Alp-1/GDP_software/CAD Models/Individual Parts/Makerbeams/eye_plate_gs3212-05.stp

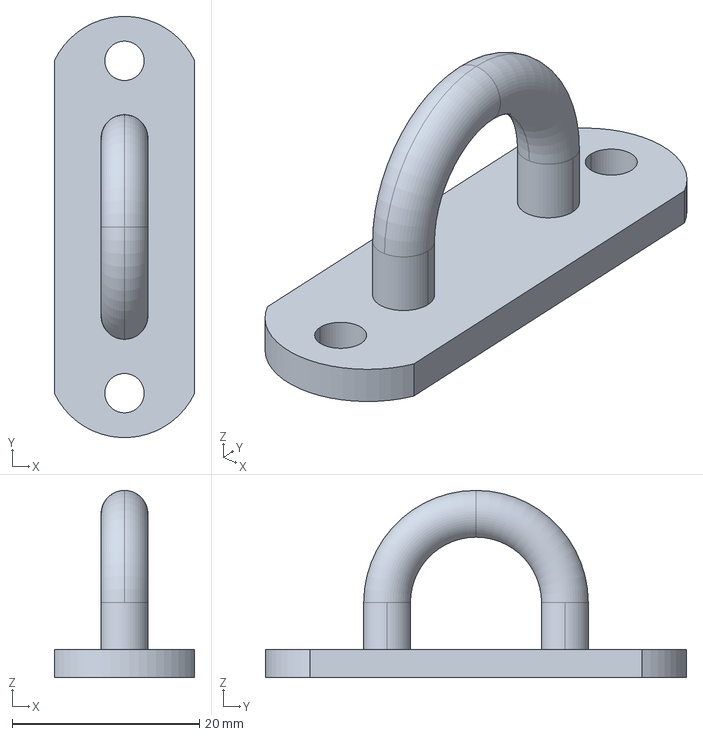
[picture p15: CAD file, 2024-10-24]
CAD Models/Individual Parts/Makerbeams/eye_plate_gs3212-05.stp
15.0 x 45.0 x 20.0 mm
