Alp-1/GDP_software/navigation/steering_basic.py

import math
import time
import numpy as np
import cv2
from pyrealsense import pyrealsense2 as rs
import json
from pymavlink import mavutil
# from dronekit import connect, VehicleMode, LocationGlobalRelative
from dronekit import *
import mav_listener
# Connect to the vehicle
mavlink_connection = mavutil.mavlink_connection('/dev/ttyAMA0', baud=57600)
mavlink_connection.wait_heartbeat()
print("Heartbeat from MAVLink system (system %u component %u)" % (
mavlink_connection.target_system, mavlink_connection.target_component))
vehicle = connect('/dev/ttyAMA0', wait_ready=False, baud=57600)

# Threshold for what we consider an obstacle (in meters)
obstacle_threshold = 1.0

def send_ned_velocity(velocity_x, velocity_y, velocity_z, duration):
    """
    Move vehicle in direction based on specified velocity vectors.
    """
    msg = vehicle.message_factory.set_position_target_local_ned_encode(
        0,       # time_boot_ms (not used)
        0, 0,    # target system, target component
        mavutil.mavlink.MAV_FRAME_BODY_OFFSET_NED, # frame
        0b0000111111000111, # type_mask (only speeds enabled)
        0, 0, 0, # x, y, z positions (not used)
        velocity_x, velocity_y, velocity_z, # x, y, z velocity in m/s
        0, 0, 0, # x, y, z acceleration (not supported yet, ignored in GCS_Mavlink)
        0, 0)    # yaw, yaw_rate (not supported yet, ignored in GCS_Mavlink)

    # send command to vehicle on 1 Hz cycle
    for x in range(0,duration):
        vehicle.send_mavlink(msg)
        time.sleep(1)

def send_ned_yaw_pymavlink(velocity_x, velocity_y, velocity_z, yaw, duration):
    """
    Move vehicle in direction based on specified velocity vectors using pymavlink.
    """
    for _ in range(duration):
        mavlink_connection.mav.set_position_target_local_ned_send(
            0,  # time_boot_ms (not used)
            mavlink_connection.target_system,  # target system
            mavlink_connection.target_component,  # target component
            mavutil.mavlink.MAV_FRAME_BODY_OFFSET_NED,  # frame
            0b0000111111000111,  # type_mask (only speeds enabled)
            0, 0, 0,  # x, y, z positions (not used)
            velocity_x, velocity_y, velocity_z,  # x, y, z velocity in m/s
            0, 0, 0,  # x, y, z acceleration (not supported yet, ignored in GCS_Mavlink)
            math.radians(yaw), 0)  # yaw, yaw_rate
        time.sleep(1)

def send_ned_yaw_pymavlink_once(velocity_x, velocity_y, velocity_z, yaw):
    """
    Move vehicle in direction based on specified velocity vectors using pymavlink.
"""
    mavlink_connection.mav.set_position_target_local_ned_send(
        0,  # time_boot_ms (not used)
        mavlink_connection.target_system,  # target system
        mavlink_connection.target_component,  # target component
        mavutil.mavlink.MAV_FRAME_BODY_OFFSET_NED,  # frame
        0b100111111111,  # type_mask (only speeds enabled)
        0, 0, 0,  # x, y, z positions (not used)
        velocity_x, velocity_y, velocity_z,  # x, y, z velocity in m/s
        0, 0, 0,  # x, y, z acceleration (not supported yet, ignored in GCS_Mavlink)
        math.radians(yaw), 0)  # yaw, yaw_rate

def send_ned_pymavlink(velocity_x, velocity_y, velocity_z):
    mavlink_connection.mav.set_position_target_local_ned_send(
        0,  # time_boot_ms (not used)
        mavlink_connection.target_system,  # target system
        mavlink_connection.target_component,  # target component
        mavutil.mavlink.MAV_FRAME_BODY_OFFSET_NED,  # frame
        0b110111100111 ,  # type_mask (only speeds enabled)
        0, 0, 0,  # x, y, z positions (not used)
        velocity_x, velocity_y, velocity_z,  # x, y, z velocity in m/s
        0, 0, 0,  # x, y, z acceleration (not supported yet, ignored in GCS_Mavlink)
        0, 0)  # yaw, yaw_rate

def spin_rover(duration, left_speed, right_speed):
    
    start_time = time.time()
    while time.time() - start_time < duration:
        left_speed = 1200
        right_speed = 1500
        override_rc_channels(left_speed,right_speed,0,0)
        time.sleep(0.1)

    # Stop the rover after spinning
    override_rc_channels(1500, 1500, 0, 0)

def wait_for_turn_completion(yaw_angle, turn_rate=30):
    """
    Wait for the rover to complete its turn.

    Parameters:
    yaw_angle (float): The yaw angle in degrees.
    turn_rate (float): Estimated turn rate in degrees per second.
    """
    turn_time = abs(yaw_angle / turn_rate)
    send_ned_yaw_pymavlink(0, 1, 0, 90, turn_time)
    

def turn_rover(yaw_angle, relative=True):
    """
    Turn the rover by a specified angle.

    Parameters:
    yaw_angle (float): The yaw angle in degrees. Positive values turn right, negative values turn left.
    relative (bool): If True, the turn is relative to the current heading.
    """
    set_yaw_angle(yaw_angle, relative)
    wait_for_turn_completion(yaw_angle)



def set_yaw_angle(yaw_angle, relative=False):
    """
    Set the yaw angle of the vehicle.

    Parameters:
    yaw_angle (float): The yaw angle in degrees.
    relative (bool): Set to True if the provided yaw angle is relative to the current heading.
    """
    if relative:
        is_relative = 1  # yaw relative to direction of travel
    else:
        is_relative = 0  # yaw is an absolute angle

    # Convert yaw angle to a valid range
    yaw_angle = yaw_angle % 360

    # Send COMMAND_LONG to set the yaw angle
    mavlink_connection.mav.command_long_send(
        mavlink_connection.target_system,  # target_system
        mavlink_connection.target_component,  # target_component
        mavutil.mavlink.MAV_CMD_CONDITION_YAW,  # command
        0,  # confirmation
        yaw_angle,  # param 1: yaw angle in degrees
        0,  # param 2: yaw speed (not used)
        1,  # param 3: direction (-1: CCW, 1: CW)
        is_relative,  # param 4: relative or absolute
        0, 0, 0  # params 5-7 (not used)
    )

# Function to be called whenever HEARTBEAT messages are received
def heartbeat_listener(self, name, message):
    print("Heartbeat received")
    print("Base Mode: {}".format(message.base_mode))
    print("Custom Mode: {}".format(message.custom_mode))

# Add the listener for the heartbeat message
#vehicle.add_message_listener('HEARTBEAT', heartbeat_listener)
# Global variable for the RealSense profile
profile = None


# Function to override RC channels
# def override_rc(channels):
#     channel_values = [0] * 8  # there are eight RC channels on most systems
#     for channel, value in channels.items():
#         channel_values[channel - 1] = value  # channels are 1-indexed in MAVLink
#     vehicle.channels.overrides = channel_values


#Create a message listener for all messages.
# @vehicle.on_message('*')
def listener(self, name, message):
    print ('message: %s' % message)


# Function to clear RC overrides
def override_rc_channels(ch1, ch2, ch3, ch4):
    """
    Override RC channels using pymavlink.
    ch1, ch2, ch3, ch4: Channel values (1000 to 2000)
    """
    mavlink_connection.mav.rc_channels_override_send(
        mavlink_connection.target_system,  # target_system
        mavlink_connection.target_component,  # target_component
        ch1, ch2, ch3, ch4, 0, 0, 0, 0)  # channels 1-8 (set channels 5-8 to 0)



# Initialize RealSense pipeline and profile
def initialize_realsense():
    global profile
    pipeline = rs.pipeline()
    config = rs.config()
    config.enable_stream(rs.stream.color, 848, 480, rs.format.bgr8, 60)  # RGB stream
    config.enable_stream(rs.stream.depth, 848, 480, rs.format.z16, 60)  # Depth stream
    config.enable_stream(rs.stream.accel, rs.format.motion_xyz32f, 200)  # Accelerometer data
    config.enable_stream(rs.stream.gyro, rs.format.motion_xyz32f, 400)  # Gyroscope data
    profile = pipeline.start(config)

    sensor = profile.get_device().query_sensors()[1]
    sensor.set_option(rs.option.enable_auto_exposure, False)
    sensor.set_option(rs.option.exposure, 78.0)
    sensor.set_option(rs.option.gain, 90.0)

    depth_sensor = profile.get_device().query_sensors()[0]
    # depth_sensor.set_option(rs.option.visual_preset,4) #high density preset, medium density is 5. doesn't work rn, maybe because of no advanced mode on pi?
    return pipeline, profile


def apply_filters(depth_frame):
    decimation = rs.decimation_filter()
    spatial = rs.spatial_filter()
    spatial.set_option(rs.option.holes_fill, 5)  # do I still need hole filling???
    hole_filling = rs.hole_filling_filter(2)  # use min of neighbour cells,might need changing
    threshold_filter = rs.threshold_filter(0.3, 4.0)
    depth_to_disparity = rs.disparity_transform(True)
    disparity_to_depth = rs.disparity_transform(False)

    # spatial.set_option(rs.option.holes_fill, 3) #try 5??
    frame = depth_frame
    frame = threshold_filter.process(frame)
    frame = decimation.process(frame)
    frame = depth_to_disparity.process(frame)
    frame = spatial.process(frame)
    frame = disparity_to_depth.process(frame)
    frame = hole_filling.process(frame)
    return frame


def get_new_images():
    frames = pipeline.wait_for_frames()
    depth_frame = frames.get_depth_frame()
    color_frame = frames.get_color_frame()
    if not depth_frame or not color_frame:
        print("problems")

    color_image = np.asanyarray(color_frame.get_data())
    depth_frame = apply_filters(depth_frame)
    depth_image = np.asanyarray(depth_frame.get_data()) * depth_scale

    # num_zeros = np.count_nonzero(depth_image == 0)
    # print(f"Number of zero values in depth image:{num_zeros}")
    return depth_image, color_image


# Specify the width of the rover in meters
rover_width = 0.5  # Adjust to your rover's width

def obstacle_ahead(depth_image, depth_scale):
    depth_image= depth_image * depth_scale

    # Calculate the size of the central square
    central_width = depth_image.shape[1] // 3
    central_height = depth_image.shape[0] // 4

    # Calculate the starting indices for the central square
    start_row = (depth_image.shape[0] - central_height) // 2
    start_col = (depth_image.shape[1] - central_width) // 2

    # Select the central square
    central_square = depth_image[start_row:start_row + central_height, start_col:start_col + central_width]

    # Create a masked array where 0 values are masked
    masked_array = np.ma.masked_where(central_square == 0, central_square)

    # Find the minimum value while excluding masked values (0s)
    min_value_without_zeros = np.min(masked_array)
    if min_value_without_zeros<obstacle_threshold:
        return True
    else:
        return False

# Function to find a clear path and calculate its direction
def find_clear_path_and_calculate_direction(depth_image, depth_scale, rover_width):
    # Convert depth image to meters
    depth_image_meters = depth_image * depth_scale

    # Threshold for what we consider an obstacle (in meters)
    column_means = np.mean(depth_image_meters, axis=0)
    # Find the index of the column with the highest mean
    index_of_highest_mean = np.argmax(column_means)
    angle = index_of_highest_mean / len(column_means) * 87 - (87 / 2)
    if angle>=0:
        yaw_angle = math.radians(angle)
    else:
        yaw_angle = math.radians(angle+360)
        
    # if angle>=0:
        # yaw_angle = angle
    # else:
        # yaw_angle = 360 + angle
    return yaw_angle

vegetation_threshold = 0.017
def detect_tall_vegetation(depth_image, depth_scale, vegetation_height_threshold):
    """
    Detect tall vegetation in the path using a RealSense depth image.

    Parameters:
    depth_image (ndarray): The depth image from the RealSense camera.
    depth_scale (float): The scale to convert depth units to meters.
    vegetation_height_threshold (float): The minimum height (in meters) to consider as vegetation.

    Returns:
    bool: True if tall vegetation is detected, False otherwise.
    """
    vegetation_height_threshold = 0.2 
    # Convert depth image to meters
    # depth_in_meters = depth_image * depth_scale
    depth_in_meters = depth_image
    # Define the region of interest (ROI) in the image
    # For example, you might want to focus on the lower part of the image
    roi_start_row = int(depth_in_meters.shape[0] * 0.5)  # Starting from the middle row
    roi_end_row = depth_in_meters.shape[0]  # To the end of the image
    roi = depth_in_meters[roi_start_row:roi_end_row, :]

    # Find areas in the ROI where the depth suddenly changes
    # This can be done by calculating the gradient and looking for large changes
    depth_gradient = np.abs(np.gradient(roi, axis=0))
    vegetation_mask = depth_gradient > vegetation_height_threshold

    # Detect vegetation if there are significant changes in depth
    vegetation_detected = np.any(vegetation_mask)
    print("detected")
    return vegetation_detected

def move_back(steps):
    """
    Move the rover back by a certain number of steps.
    """
    for _ in range(steps):
        send_ned_velocity(-1, 0, 0, 1)
            
# Function to navigate while avoiding obstacles
def navigate_avoiding_obstacles(depth_scale):
    obstacle_threshold = 1.0
    frames = pipeline.wait_for_frames()
    depth_frame = frames.get_depth_frame()
    if not depth_frame:
        return

    depth_image = np.asanyarray(depth_frame.get_data())
    print(vehicle.mode.name)
    if vehicle.mode.name == "AUTO" or vehicle.mode.name == "GUIDED":
        if detect_tall_vegetation(depth_image, depth_scale):
            print("Tall vegetation detected. Moving back.")
            vehicle.mode = VehicleMode("GUIDED")
            move_back(2)  # Move back 2 steps
        else:
            if obstacle_ahead(depth_image,depth_scale):
                vehicle.mode = VehicleMode("GUIDED")
                clear_path_direction = find_clear_path_and_calculate_direction(depth_image, depth_scale, rover_width)
            #print(clear_path_direction)
         
                print("obstacle ahead")
#                 current_heading = vehicle.heading

#         # Calculate new heading: turn left by 90 degrees
#                 new_heading = (current_heading + 90) % 360
#                 # Example usage
#                 # Example usage: Spin the rover for 5 seconds
# # Assuming 1000 is full reverse, 1500 is stop, and 2000 is full forward.
#                 # spin_rover(5, 1000, 2000) 

#         # Set the new yaw angle
#                 set_yaw_angle(new_heading, relative=False)

#         # Move with the specified NED velocity while turning
#                 send_ned_yaw_pymavlink(0, 1, 0, new_heading, 5)
            # send_ned_velocity(1,0,0,5)
            else:
                print("no obstacle ahead")
                vehicle.mode = VehicleMode("AUTO")
                override_rc_channels(1600, 1500, 0, 0)  # Override throttle and steering channels
import time

def detect_collision(mavlink_connection):
    """
    Detects collision by comparing rover speed from MAVLink and optical flow data.
    """
    start_time = time.time()
    collision_detected = False

    while time.time() - start_time < 5:
        # Retrieve speed data from MAVLink
        current_speed = mav_listener.get_rover_speed(mavlink_connection)  # Speed in cm/s
        print(f"speeeed:{current_speed}")
        # Retrieve optical flow data from MAVLink
        optical_flow_data = get_optical_flow_data_from_mavlink()
        print(optical_flow_data)
        # Check for near-zero optical flow and non-zero speed
        if is_near_zero(optical_flow_data) and current_speed > 0:
            collision_detected = True
            break
        time.sleep(0.1)  # Adjust time interval as needed

    if collision_detected:
        print("Collision detected. Reversing and finding another path.")
        # Implement actions after detecting collision, e.g., move_back, find_alternate_path, etc.

def is_near_zero(data, threshold=0.1):
    """
    Check if data is near zero within a given threshold.
    """
    x, y = data
    return abs(x) < threshold and abs(y) < threshold

def get_optical_flow_data_from_mavlink():
    """
    Retrieve optical flow data from MAVLink.
    """
    # Fetch optical flow data from a relevant MAVLink message
    # Example: Use flow_x and flow_y for optical flow data
    optical_flow_msg = mavlink_connection.recv_match(type='OPTICAL_FLOW', blocking=True)
    if optical_flow_msg:
        return optical_flow_msg.flow_x, optical_flow_msg.flow_y
    else:
        return 0, 0

# Implement move_back() and find_alternate_path() as needed


def wheels_are_spinning():
    left_dist1, right_dist1 = mav_listener.get_wheel_distances(mavlink_connection)
    time.sleep(0.05)
    left_dist2, right_dist2 = mav_listener.get_wheel_distances(mavlink_connection)
    left_diff = left_dist2 - left_dist1
    right_diff = right_dist2 - right_dist1
    print(f"Wheel distance difference in 50ms: {left_diff} {right_diff}")
    if left_diff>0.02 or right_diff>0.02:
        return True
    else:
        return False

def is_tall_vegetation(depth_image,speed):
    percentage_threshold = 0.5
    nr_of_pixels = depth_image.size
    print(nr_of_pixels)
    percentage = np.count_nonzero(depth_image==0) / nr_of_pixels
    print(f"percentage of pixels with 0 value:{percentage}")
    if percentage>percentage_threshold and speed > 0.35:
        return True
    else:
        return False


def is_collision(speed):
    if speed < 0.25 and wheels_are_spinning():
        return True
    else:
        return False



def calculate_distance(depth_image, y1, x1, y2, x2):
    # udist = depth_frame.get_distance(x1, y1)
    # vdist = depth_frame.get_distance(x2, y2)
    udist = depth_image[y1, x1]
    vdist = depth_image[y2, x2]

    point1 = rs.rs2_deproject_pixel_to_point(depth_intrinsics, [y1, x1], udist)
    point2 = rs.rs2_deproject_pixel_to_point(depth_intrinsics, [y2, x2], vdist)

    # euclidean distance between two points, measured in meters
    dist = math.sqrt(
        math.pow(point1[0] - point2[0], 2) + math.pow(point1[1] - point2[1], 2) + math.pow(
            point1[2] - point2[2], 2))
    # result[0]: right, result[1]: down, result[2]: forward
    return dist


def gap_size(depth_image, column):
    gap_threshold = 0.4
    # start_row = depth_image.shape[0] // 2
    width_left = column
    width_right = column
    height_up = depth_image.shape[0] // 2

    square_height = depth_image.shape[0] // 10
    # square_width = column_width
    start_row = (depth_image.shape[0] - square_height) // 2
    end_row = start_row + square_height
    gap_width = 9999.0
    for row in range(start_row, end_row+1):
        width_left = column
        width_right = column
        if depth_image[row,column] != 0:
            while width_left > 1:
                difference = depth_image[row, width_left] - depth_image[row, width_left - 1]
                if difference > gap_threshold and depth_image[row, width_left - 1] < (2 * obstacle_threshold) and \
                        depth_image[row, width_left - 1] < depth_image[row, column] and depth_image[row, width_left - 1] !=0:
                    break
                else:
                    width_left -= 1
            width_left -= 1

            while width_right < (depth_image.shape[1] - 2):
                difference = depth_image[row, width_right] - depth_image[row, width_right + 1]
                if difference > gap_threshold and depth_image[row, width_right + 1] < (2 * obstacle_threshold) and \
                        depth_image[row, width_right + 1] < depth_image[row, column] and depth_image[row, width_right + 1]!=0:
                    break
                else:
                    width_right += 1
            width_right += 1
            width = calculate_distance(depth_image, row, width_left, row, width_right)
            gap_width = min(width,gap_width)

    while height_up > 1:
        difference = depth_image[height_up, column] - depth_image[height_up - 1, column]
        if difference > gap_threshold and depth_image[height_up - 1, column] < (2 * obstacle_threshold) and depth_image[
            height_up - 1, column] < depth_image[row, column] and depth_image[height_up - 1, column] != 0:
            break
        else:
            height_up -= 1
    height_up -= 1

    gap_height = calculate_distance(depth_image, row, column, height_up, column)
    print(f"gap boundary pixels:{width_left} {width_right}")
    print(f"GAP: height from camera:{gap_height} width:{gap_width}")
    return gap_height, gap_width


# Main execution loop
try:
    pipeline, profile = initialize_realsense()
    depth_sensor = profile.get_device().first_depth_sensor()
    depth_scale = depth_sensor.get_depth_scale()

    frames = pipeline.wait_for_frames()
    prof = frames.get_profile()
    depth_intrinsics = prof.as_video_stream_profile().get_intrinsics()
    print("Depth Scale is: ", depth_scale)
    detect_collision(mavlink_connection)
    vehicle.armed = True
    # turn_rover(90, relative=True)
    print(vehicle.mode)
    while True:
        current_speed = mav_listener.get_rover_speed(mavlink_connection)
        current_speed /= 100
        print(f"current speed:{current_speed}")

        depth_image,color_image = get_new_images()
        if is_tall_vegetation(depth_image,current_speed):
            print("TALL VEGETATION")

        if is_collision(current_speed):
            print("COLLISION")
        gap_size(depth_image,depth_image.shape[1]//2)
        # if both -> go back abit. if only one of the, different
        # how to interpret encoder data
        # detect_collision(mavlink_connection)
        # detect_tall_vegetation(depth_image,depth_scale,0.017)

        time.sleep(0.2)
except KeyboardInterrupt:
    print("Script terminated by user")

finally:
    # clear_rc_overrides()
    pipeline.stop()
    cv2.destroyAllWindows()
    vehicle.close()
    mavlink_connection.close()
    print("Connection closed.")
