Alp-1/GDP_software/low_level_control/motor_controller/motor_sensor.py

from machine import Pin, ADC

from motor_controller.encoder import Encoder


class MotorSensing:
    """Class to sense the parameters of a motor"""

    PPR = 2448  # Pulses per revolution of the encoder (12*4*51)

    def __init__(
        self,
        encoder_out_A: int,
        sm_no: int,
        adc_in: int,
        invert_current: bool = False,
    ):
        """Initialise motor feedback components.

        Parameters
        ----------
        encoder_out_A: int
            The output A of the encoder.
            The second pin (Output B) is assumed to be encoder_out_A + 1
        sm_no: int
            The state machine number to use for the encoder pio
        adc_in: int
            The ADC pin to use for current sensing
        invert_current: bool
            Set to True if the current sensor is inverted

        """
        # Define the pins for the inputs
        ENCODER_OUT_A = Pin(encoder_out_A, Pin.IN, Pin.PULL_DOWN)
        self.encoder = Encoder(sm_no, ENCODER_OUT_A)
        self.current_sensor = ADC(adc_in)
        self.invert_current = invert_current

        self.no_of_samples = 256 * 4
        self.offset_u16 = 0
        self.calibrate_adc()

    def calibrate_adc(self):
        """Calibrate the ADC by finding the zero current adc val
        (i.e. the midpoint of the adc range in theory)
        """
        average_u16 = 0
        for _ in range(self.no_of_samples):
            average_u16 += self.current_sensor.read_u16()
        self.offset_u16 = average_u16 / self.no_of_samples

    @property
    def rpm(self):
        result = self.encoder.freq() * 60 / self.PPR
        # print("Freq: {}".format(self.encoder.freq()))
        # print("RPM: {}".format(result))
        return result

    @property
    def current(self):
        """Get the current of the motor (A).

        For ACS711EX (+-31A), the sensitivity is 45 mV/A for 3.3V supply.

        45mV/A is derived from 3.3V/73.3A (Refer to https://www.pololu.com/product/2453)

        Perform averaging for better accuracy.
        """

        average_u16 = 0
        for _ in range(self.no_of_samples):
            average_u16 += self.current_sensor.read_u16()
        average_u16 /= self.no_of_samples
        vout = (average_u16 - self.offset_u16) * 3.3 / 65535
        if self.invert_current:
            vout = -vout
        return vout / 0.045
