Alp-1/GDP_software/low_level_control/central_hub/main.py

from central_hub.central_hub import main
import asyncio

while True:
    try:
        asyncio.run(main())
    except Exception as e:
        print(e)
    finally:
        print(asyncio.current_task().coro)
        asyncio.new_event_loop()
