Alp-1/GDP_software/navigation/geometric_map.py

import copy
import math

import open3d as o3d
import numpy as np
from pyrealsense import pyrealsense2 as rs
import time
import scipy
import cv2
# cell_height = 120
# cell_width = 212
# grid_n = 4
# grid_m = 4
from matplotlib import pyplot as plt

# cell_height = 60
# cell_width = 106 #miert??
grid_n = 1
grid_m = 4

#!!!changed: 10x10 grid
def direction_to_euler_angles(direction):
    # Normalize the direction vector
    normalized_direction = direction / np.linalg.norm(direction)

    # Calculate pitch angle
    pitch_rad = np.arcsin(normalized_direction[2])
    pitch_deg = np.degrees(pitch_rad)

    # Calculate yaw angle
    yaw_rad = np.arctan2(normalized_direction[1], normalized_direction[0])
    yaw_deg = np.degrees(yaw_rad)

    return pitch_deg, yaw_deg

def get_slope_grid(depth_image,depth_intrinsics,angles):
    rotation_matrix = o3d.geometry.get_rotation_matrix_from_zyx((math.radians(angles[0]),0,math.radians(angles[2])))
    cell_height = int(depth_image.shape[0] // 1)
    cell_width = int(depth_image.shape[1] // 4)
    depth_grid = scipy.sparse.bsr_matrix(depth_image, blocksize=(cell_height, cell_width), dtype=np.float32).data
    np_grid = np.asanyarray(depth_grid)
    i = 0
    j = 0
    slope_grid = np.zeros((grid_n, grid_m))
    pcds = []
    central_outliers = np.empty((0, 3))
    for cell in np_grid:
        image_o3d = o3d.geometry.Image(cell.astype(np.float32))
        pcd = o3d.geometry.PointCloud.create_from_depth_image(
            image_o3d, o3d.camera.PinholeCameraIntrinsic(depth_intrinsics.width, depth_intrinsics.height,
                                                         depth_intrinsics.fx, depth_intrinsics.fy,
                                                         depth_intrinsics.ppx, depth_intrinsics.ppy))
        pcd.transform([[1, 0, 0, 0], [0, -1, 0, 0], [0, 0, -1, 0], [0, 0, 0, 1]])  # flip it
        downpcd = pcd #.voxel_down_sample(voxel_size=0.02)

        adjusted_pcd = copy.deepcopy(downpcd)
        adjusted_pcd.rotate(rotation_matrix)
        # pcds.append(adjusted_pcd)
        if len(downpcd.points)>30:
            plane_model, inliers = adjusted_pcd.segment_plane(distance_threshold=0.005,ransac_n=3,num_iterations=1000)
            [a, b, c, d] = plane_model

            inlier_cloud = pcd.select_by_index(inliers)
            inlier_cloud.paint_uniform_color([1.0, 0, 0])
            outlier_cloud = pcd.select_by_index(inliers, invert=True)

            if j==1 or j==2:
                outlier_points = np.asarray(outlier_cloud.points)
                # print(f'outliers shape:{outlier_points.shape}')
                central_outliers = np.vstack((central_outliers, outlier_points))

                # Find the index of the smallest number in each sublist
                min_indices = np.argmin(outlier_points, axis=0)

                # Extract the sublist with the smallest number for each element
                result_rows = outlier_points[min_indices, np.arange(outlier_points.shape[1])]

                # print(f'nr of outlier points: {len(outlier_points)}')
            if a == 0:
                pitch_degrees = 90
            else:
                # pitch_cos = math.cos(b / math.sqrt(math.pow(a, 2) + math.pow(b, 2) + math.pow(c, 2)))
                # print(pitch_cos)
                # pitch = math.acos(pitch_cos)
                # print(f'radians:{pitch}')
                # pitch_degrees = math.degrees(pitch)
                pitch_degrees,_ = direction_to_euler_angles(np.array([a,b,c]))
                # print(f"{i} {j}: {a:.2f}x + {b:.2f}y + {c:.2f}z + {d:.2f} = 0   pitch:{pitch_degrees}")

        else:
            pitch_degrees = 90
        slope_grid[i, j] = pitch_degrees

        if j == (grid_m - 1):
            i += 1
            j = 0
        else:
            j += 1
    central_outliers[:, 2] *= -1

    return slope_grid[0], central_outliers
